mazls/hexagon-desk/Epoxy Casting/pxl_20220501_133700167.jpg

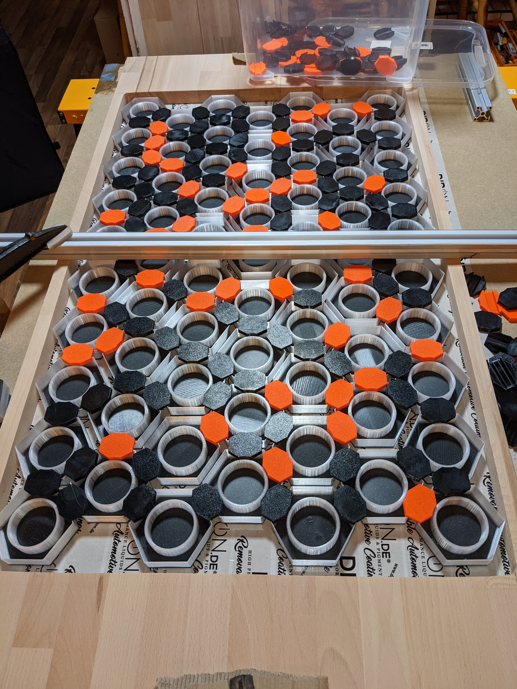
Epoxy Casting/pxl_20220501_133700167.jpg
