mazls/hexagon-desk/img/PXL_20221125_150522842.jpg

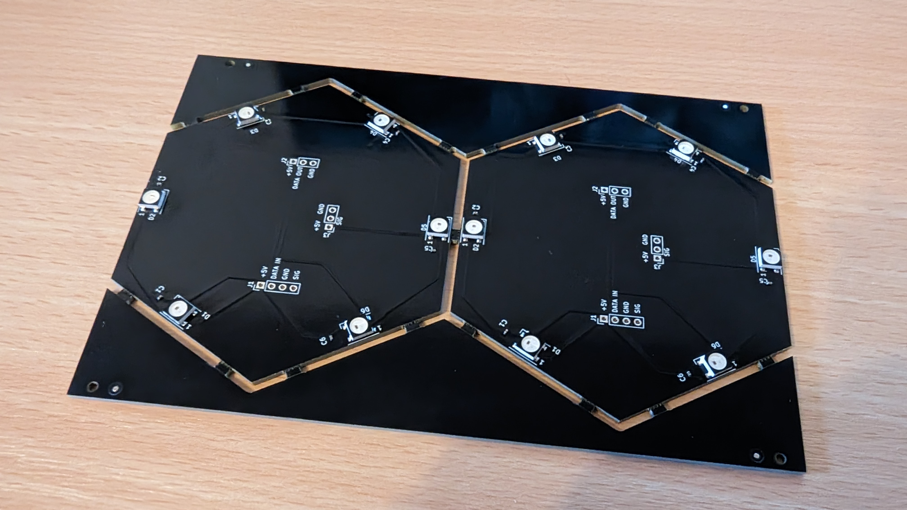
img/PXL_20221125_150522842.jpg
