mazls/hexagon-desk/img/PXL_20221125_150549323.jpg

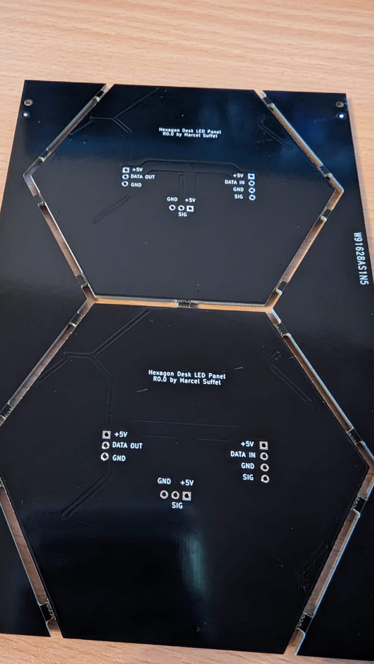
img/PXL_20221125_150549323.jpg
