mazls/hexagon-desk/img/PXL_20221125_150715876.jpg

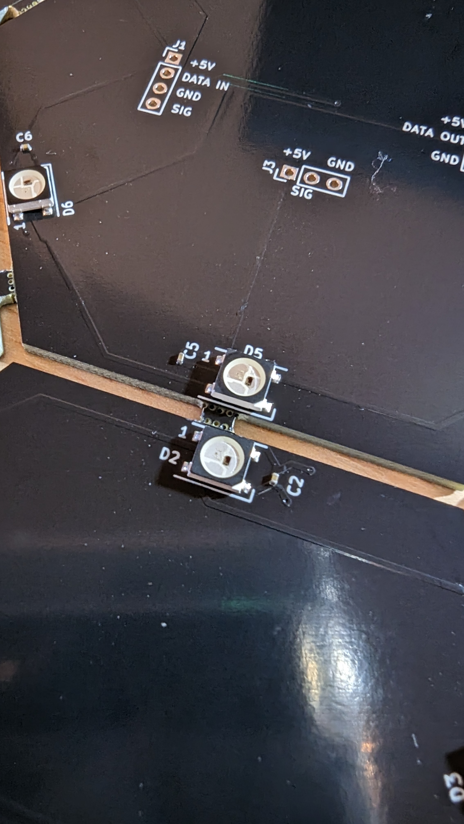
img/PXL_20221125_150715876.jpg
