mazls/hexagon-desk/img/PXL_20221127_131424585.jpg

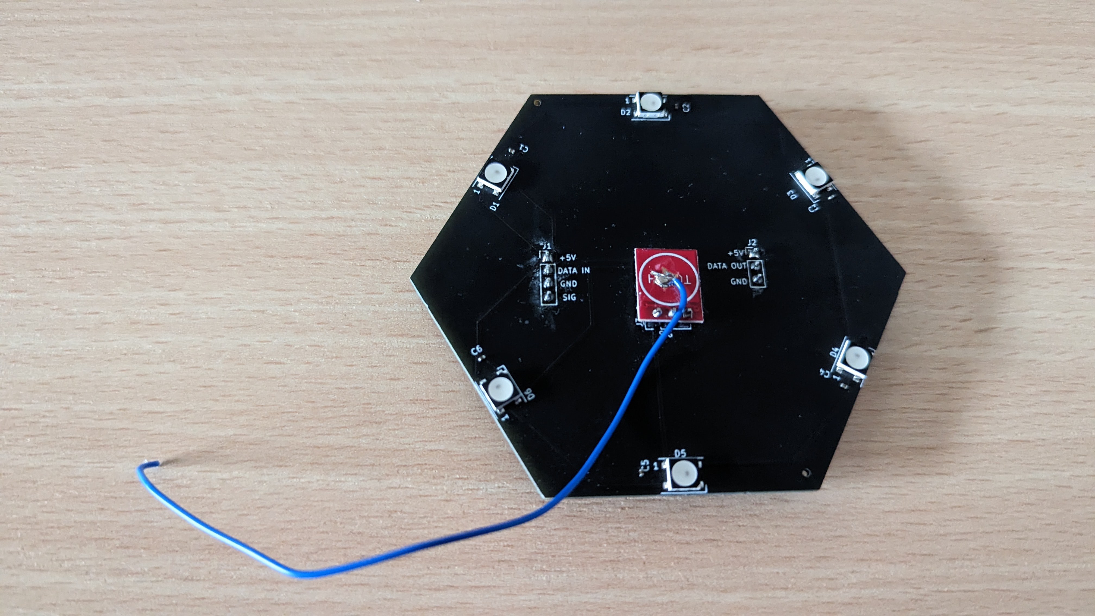
img/PXL_20221127_131424585.jpg
