mazls/hexagon-desk/img/PXL_20221127_131545157.jpg

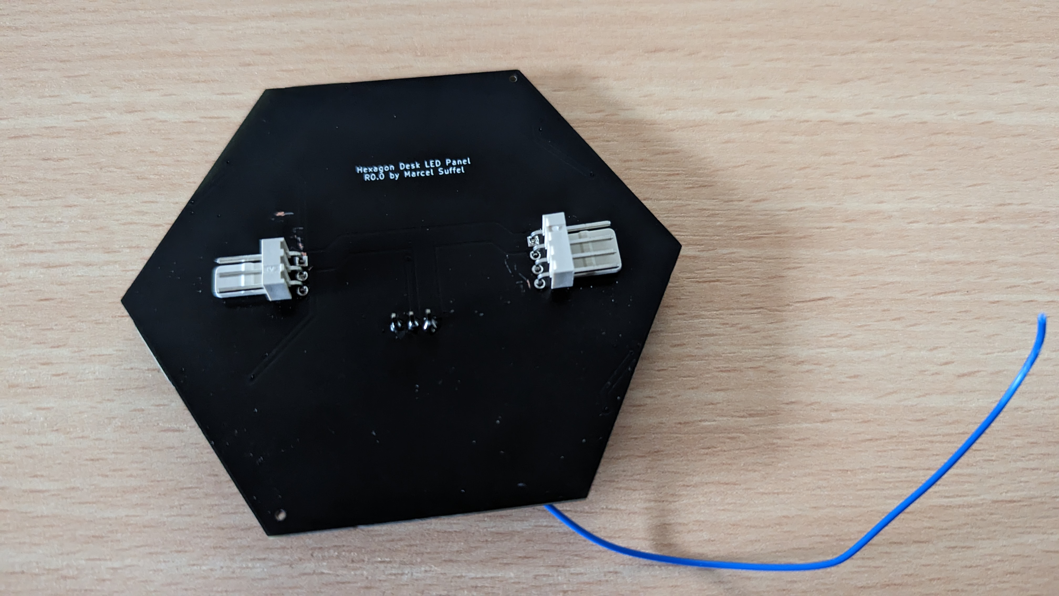
img/PXL_20221127_131545157.jpg
